rrainey/tempo-bt/images/Tempo-BT-axes.png

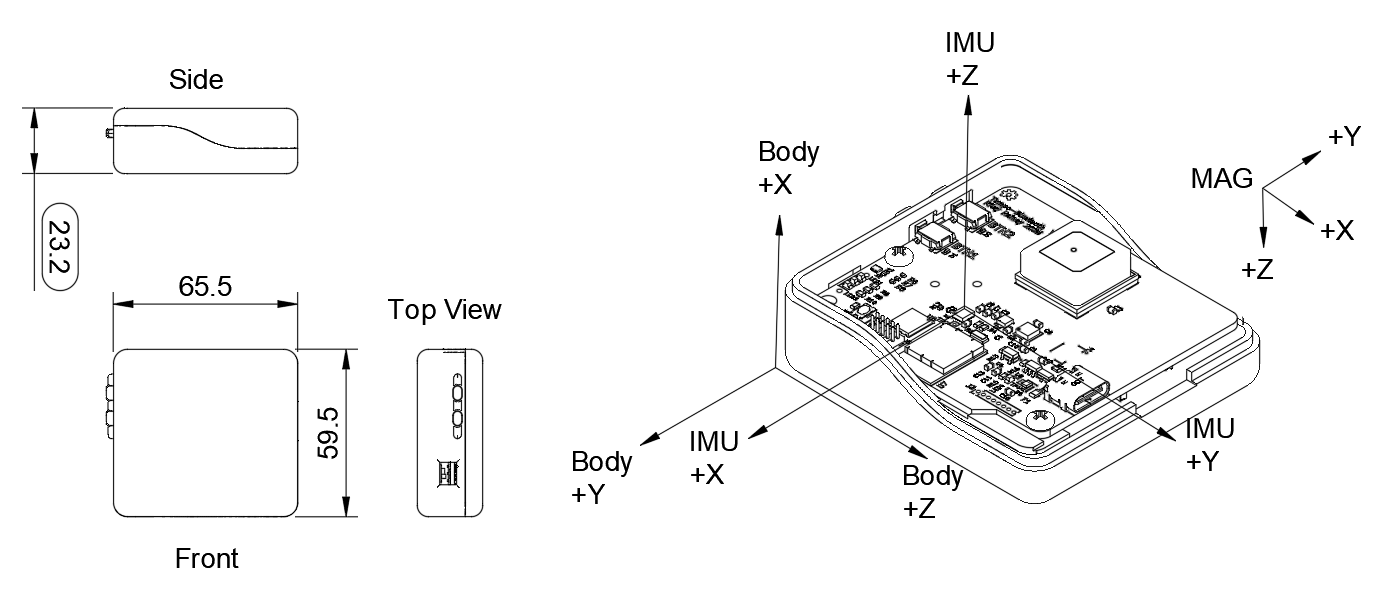
images/Tempo-BT-axes.png
