rrainey/tempo-bt/hardware/tempo-bt/tempo-bt.kicad_sch

## KiCad design hardware/tempo-bt/tempo-bt.kicad_sch (2026-01-11)

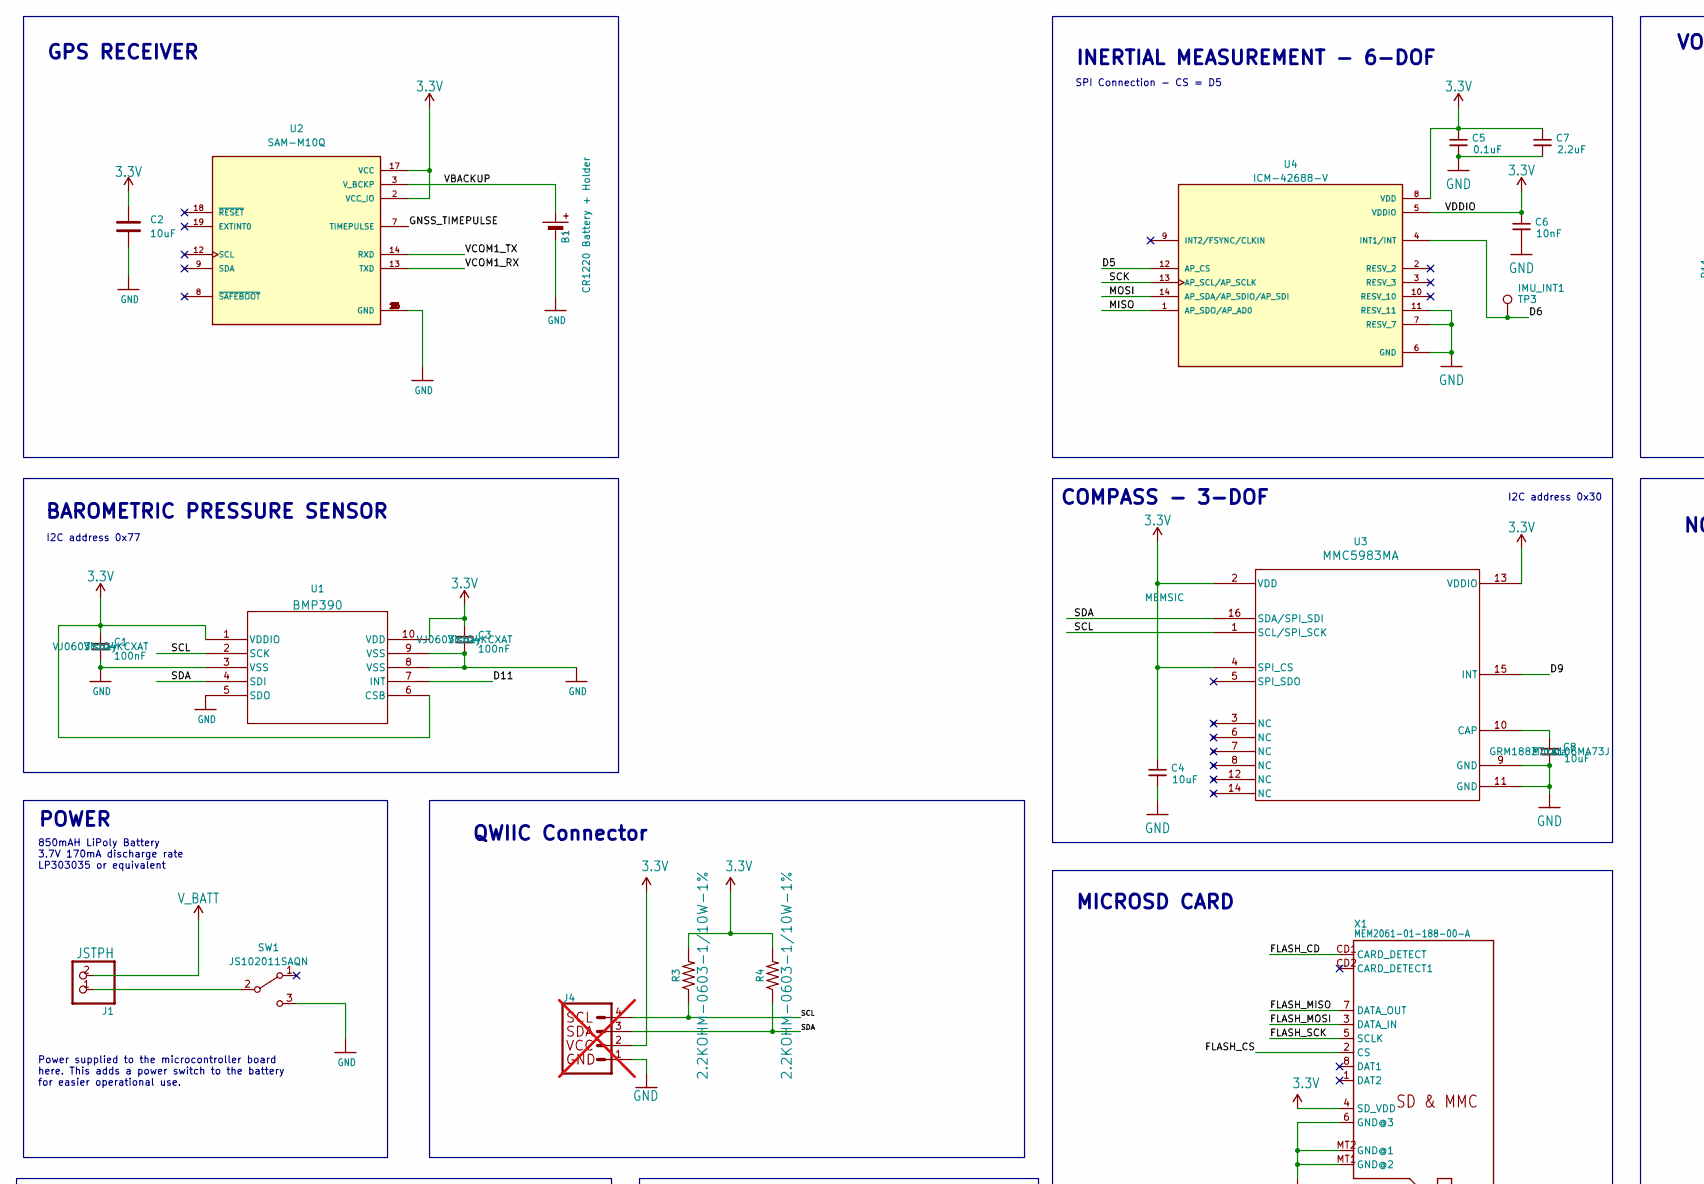
[picture p14: schematic tempo-bt.kicad_sch, part in row 1, column 1]

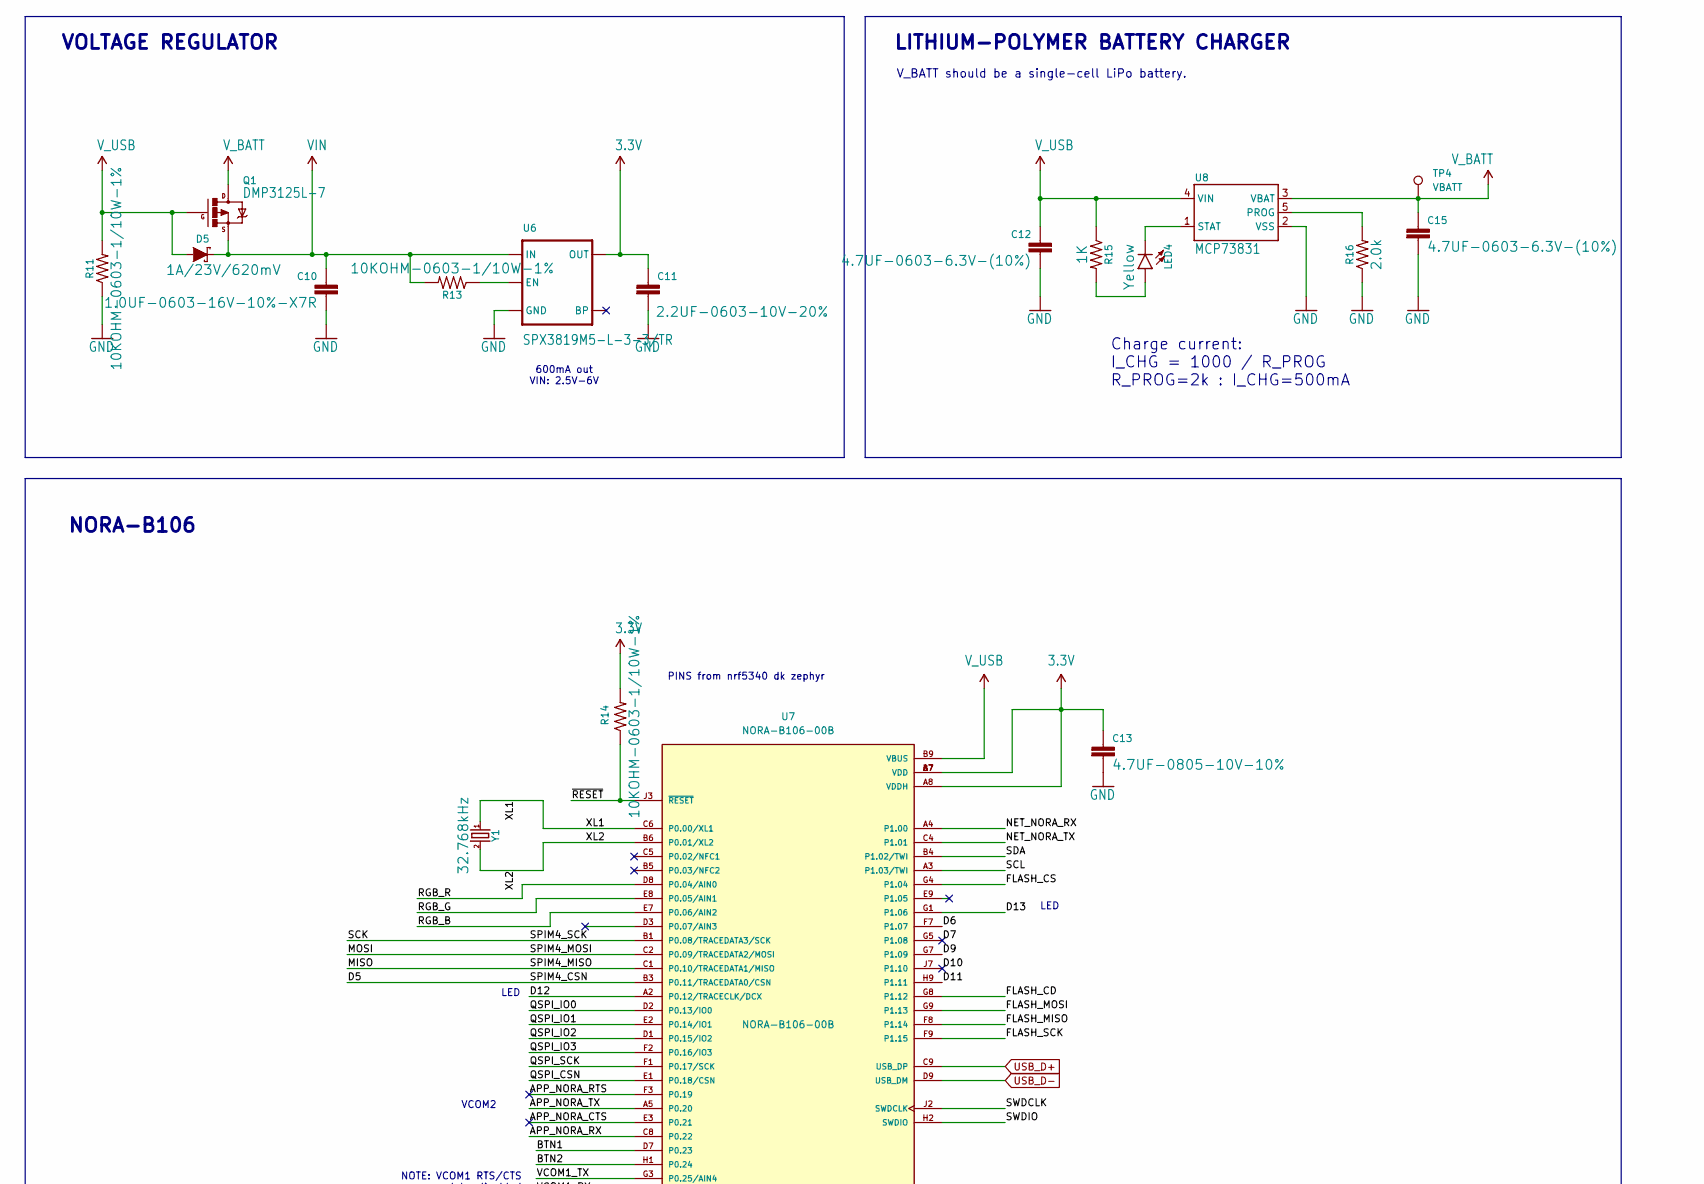
[picture p15: schematic tempo-bt.kicad_sch, part in row 1, column 2]

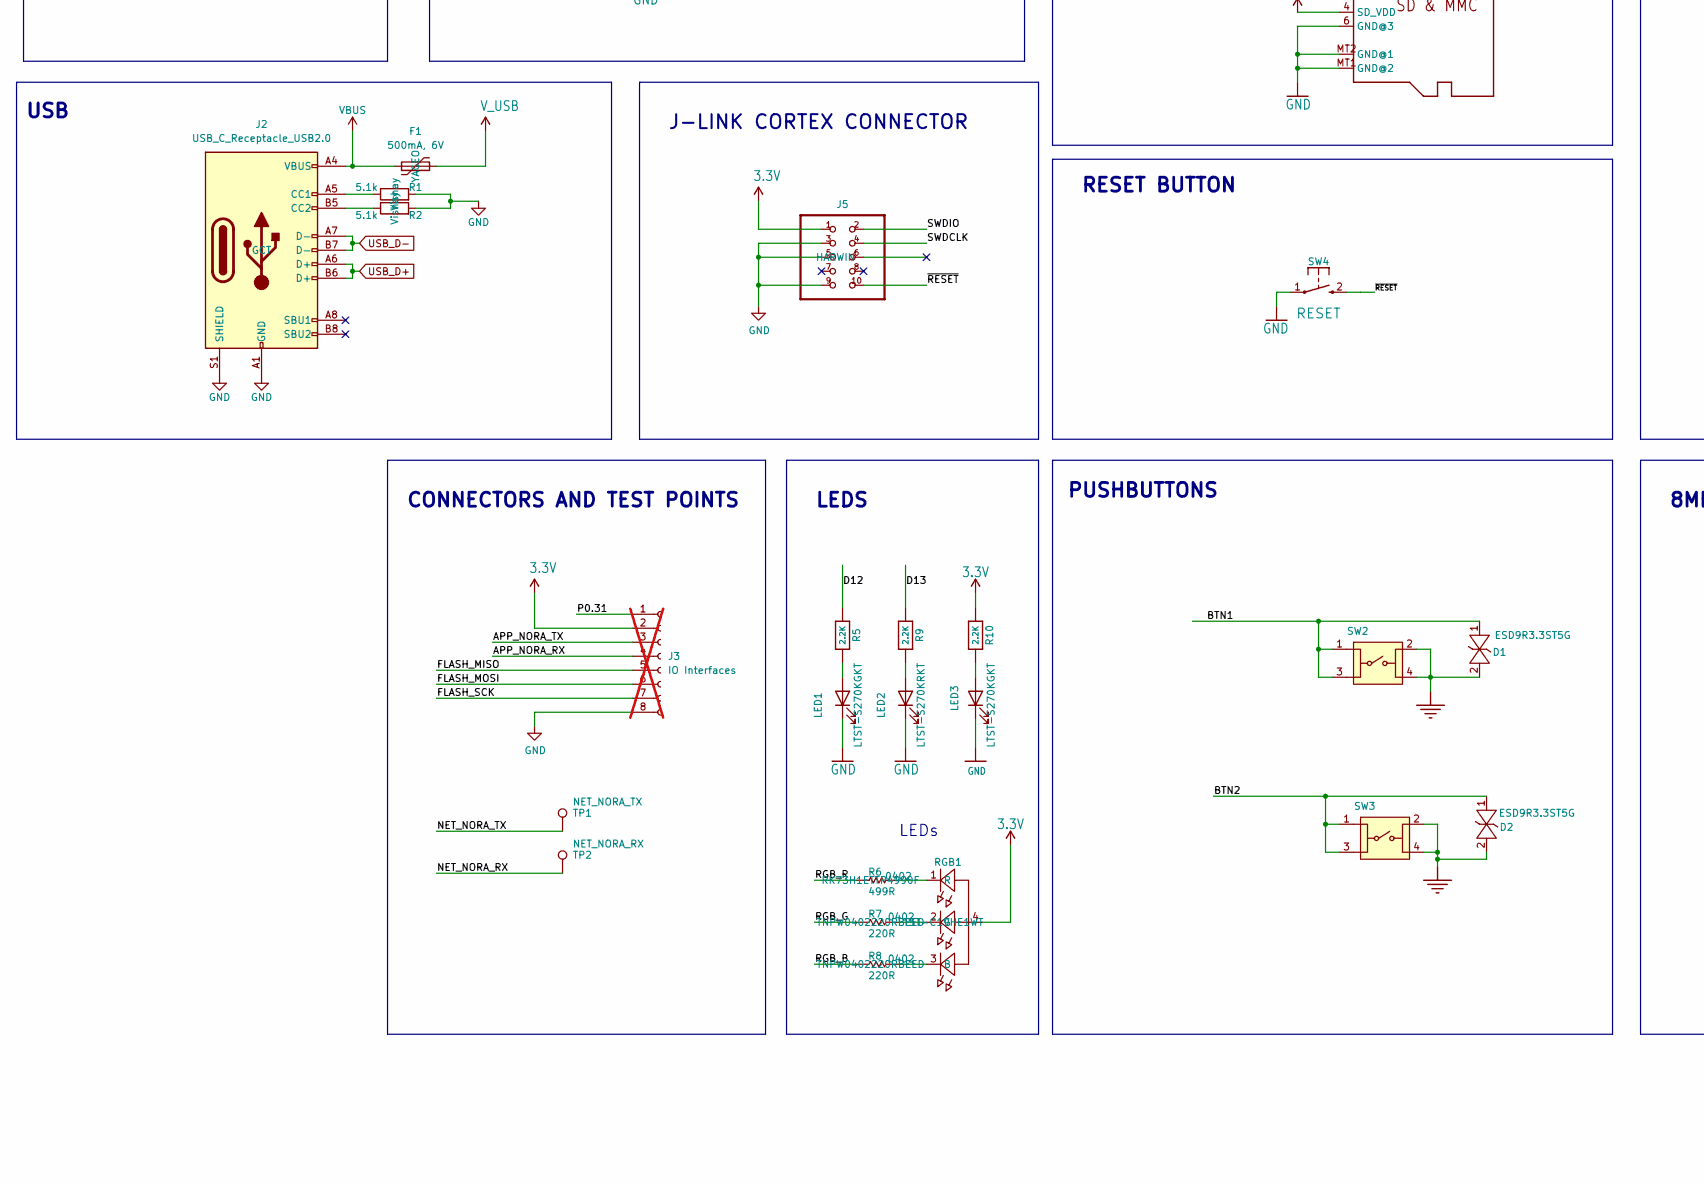
[picture p16: schematic tempo-bt.kicad_sch, part in row 2, column 1]

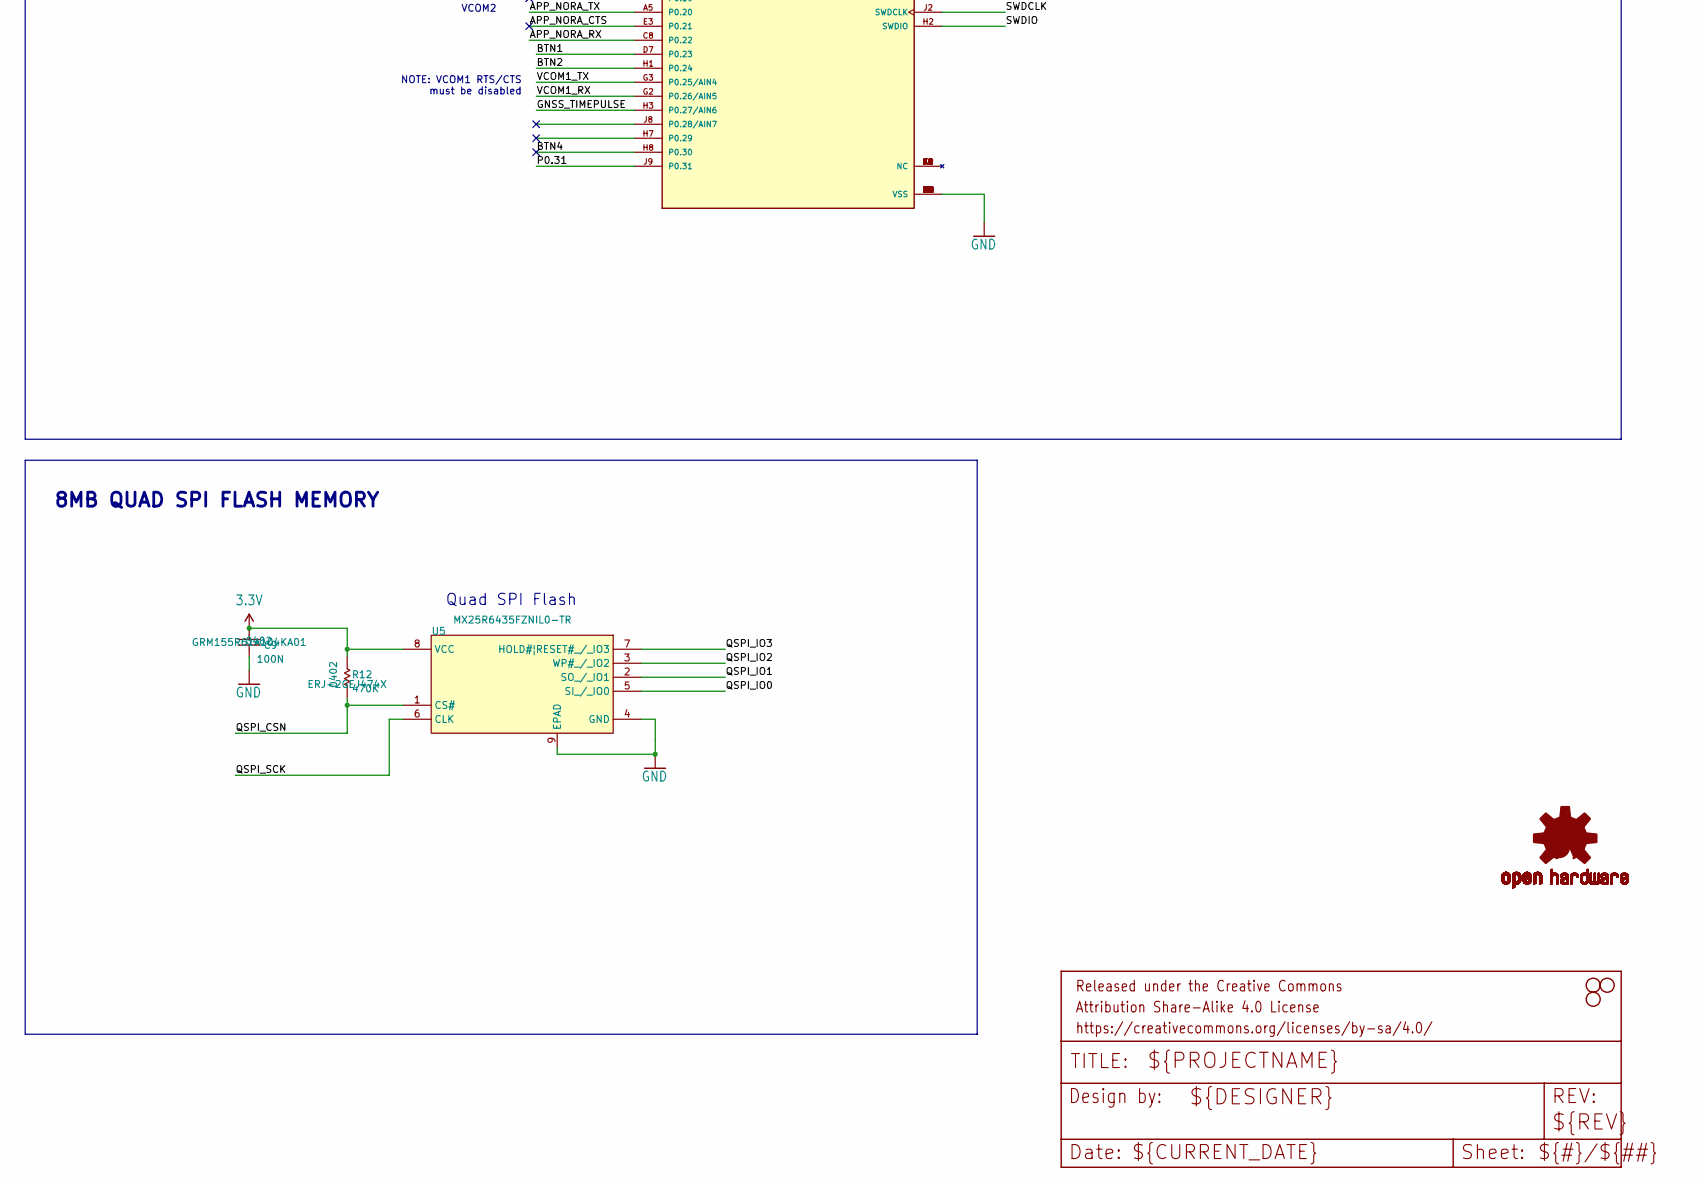
[picture p17: schematic tempo-bt.kicad_sch, part in row 2, column 2]

Parts:
B1: 1056TR; CR1220-2; MPN 1056TR
C1, C3: 100nF; C_0603_1608Metric; MPN VJ0603Y104KCXAT
C2, C4, C8: 10uF; C_0603_1608Metric; MPN GRM188Z71A106MA73J
C5: 0.1uF; C_0603_1608Metric; MPN GRT033C81A104KE01D
C6: 10nF; C_0603_1608Metric; MPN CGA3E2X7R1H103K080AE
C7: 2.2uF; C_0603_1608Metric; MPN GRM188R71A225KE15D
C9: 100nF; C_0402_1005Metric; TOLERANCE 10%; MAX VOLTAGE 10V; PART NUMBER UBXH01-2021002
C10: 1.0UF-0603-16V-10%-X7R; C_0603_1608Metric; MPN 0603DC105KAT2A
C11: 2.2UF-0603-10V-20%; C_0603_1608Metric; MPN GRM188Z71C225KE43D
C12, C15: 4.7UF-0603-6.3V-(10%); C_0603_1608Metric; MPN GRM188Z71A475KE15D
C13: 4.7UF-0805-10V-10%; 0805; MPN GRM21BR71A475KE51L
D1, D2: UBXH07-0000034${DNP}; D_SOD-923; PART NUMBER UBXH07-0000034
D5: 1A/23V/620mV; SOD-323; MPN BAT20JFILM
F1: 500mA, 6V; Fuse_0805_2012Metric; MPN SMD0805B050TF; JLCPCB Part # C269104
FRAME1: FRAME-LETTER; CREATIVE_COMMONS
H1, H2, H3: STAND-OFFTIGHT; STAND-OFF-TIGHT
J1: JSTPH; JSTPH2; Manufacturer Part S2B-PH-SM4-TB
J2: USB_C_Receptacle_USB2.0; GCT-USB4105-GF-A modified-USB-C 16P; MPN USB4105-GF-A-120; JLCPCB Part # C168688
J3: IO Interfaces; PinHeader_1x08_P1.27mm_Vertical; not fitted
J4: QWIIC_CONNECTORJS-1MM; JST04_1MM_RA; MPN SM04B-SRSS-TB; not fitted
J5: 2x5 PTH ARM CORTEX DEBUG; 2X5-PTH-1.27MM-NO_SILK; MPN M50-3500542
LED1, LED3: LTST-S270KGKT; LED_0603_1608Metric; MPN LTST-S270KGKT
LED2: LTST-S270KRKT; LED_0603_1608Metric; MPN LTST-S270KRKT
LED4: Yellow; LED-0603; MPN LTST-S270YKT
LOGO1: OSHW-LOGOS; OSHW-LOGO-S
Q1: DMP3125L-7; SOT23-3@1; MPN DMP3125L-7
R1, R2: 5.1k; R_0402_1005Metric; MPN RCC04025K10FKED; JLCPCB Part # C25905
R3, R4: 2.2KOHM-0603-1/10W-1%; 0603; MPN ERJ-H3EF2201V
R5, R9, R10: 2.2K; R_0603_1608Metric; MPN ERJ-H3EF2201V
R6: 499OHM-0402; R_0402_1005Metric; TOLERANCE 1%; PART NUMBER UBXH18-0000269
R7, R8: 220OHM-0402; R_0402_1005Metric; TOLERANCE 5%; PART NUMBER UBXH18-0008033
R11, R13, R14: 10KOHM-0603-1/10W-1%; 0603; MPN ERJ-H3EF1002V
R12: 470KOHM; R_0402_1005Metric; TOLERANCE 5%; PART NUMBER UBXH18-0008113
R15: 1K; 0603; MPN MR06X1001FTL
R16: 2.0k; 0603; MPN MR06X2001FTL
RGB1: LTST-C19HE1WT; MAX VOLTAGE 5V; PART NUMBER UBXH11-0000058
SW1: JS102011SAQN; MPN JS102011SAQN
SW2, SW3: PTS850; PTS850-with-bosses; PART NUMBER UBXH19-0000035
SW4: RESET; SW_Push_1P1T_NO_CK_KMR2; MPN KMR221NG LFS
TP1: NET_NORA_TX; TestPoint_Pad_1.0x1.0mm
TP2: NET_NORA_RX; TestPoint_Pad_1.0x1.0mm
TP3: IMU_INT1; TestPoint_THTPad_1.0x1.0mm_Drill0.5mm
TP4: VBATT; TestPoint_THTPad_1.0x1.0mm_Drill0.5mm
U1: BMP390; LGA10_BMP390_BOS; MPN BMP390
U2: SAM-M10Q; MODULE_SAM-M8Q-0-10; PARTREV R07
U3: MMC5983MA; MMC5983MA_MEM; MPN MMC5983MA
U4: ICM-42688-V; PQFN50P300X250X97-14N; PARTREV 1.2
U5: MX25R64; WSON-8-1EP_6x5mm_P1.27mm_EP3.4x4mm; PART NUMBER UBXH13-0000138
U6: SPX3819M5-L-3-3/TR; SOT23-5; MPN SPX3819M5-L-3-3/TR
U7: NORA-B106-00B; XCVR_NORA-B106-00B; PARTREV R05
U8: MCP73831; SOT23-5; MPN MCP73831T-4ADI/OT
X1: MEM2061-01-188-00-A; MICROSD; MPN MEM2061-01-188-00-A
Y1: 32.768kHz; CRYSTAL-SMD-3.2X1.5MM; MPN ABS07-120-32.768KHZ-T

Connections:
3.3V: C1.1, C2.1, C3.1, C4.1, C5.1, C6.1, C7.1, C9.1, C11.1, C13.1, J3.2, J4.2, J5.1, R3.2, R4.2, R10.1, R12.2, R14.2, RGB1.4 (A), U1.1 (VDDIO), U1.6 (CSB), U1.10 (VDD), U2.2 (VCC_IO), U2.17 (VCC), U3.2 (VDD), U3.4 (SPI_CS), U3.13 (VDDIO), U4.5 (VDDIO), U4.8 (VDD), U5.8 (VCC), U6.5 (OUT), U7.A7 (VDD), U7.A8 (VDDH), U7.B7 (VDD), X1.4 (SD_VDD)
APP_NORA_CTS: U7.E3 (P0.21)
APP_NORA_RTS: U7.F3 (P0.19)
APP_NORA_RX: J3.4, U7.C8 (P0.22)
APP_NORA_TX: J3.3, U7.A5 (P0.20)
BTN1: D1.1, SW2.1, SW2.3, U7.D7 (P0.23)
BTN2: D2.1, SW3.1, SW3.3, U7.H1 (P0.24)
BTN4: U7.H8 (P0.30)
D5: U4.12 (AP_CS), U7.B3 (P0.11/TRACEDATA0/CSN)
D6: TP3.1, U4.4 (INT1/INT), U7.F7 (P1.07)
D7: U7.G5 (P1.08)
D9: U3.15 (INT), U7.G7 (P1.09)
D10: U7.J7 (P1.10)
D11: U1.7 (INT), U7.H9 (P1.11)
D12: R5.1, U7.A2 (P0.12/TRACECLK/DCX)
D13: R9.1, U7.G1 (P1.06)
FLASH_CD: U7.G8 (P1.12), X1.CD1 (CARD_DETECT)
FLASH_CS: U7.G4 (P1.04), X1.2 (CS)
FLASH_MISO: J3.5, U7.F8 (P1.14), X1.7 (DATA_OUT)
FLASH_MOSI: J3.6, U7.G9 (P1.13), X1.3 (DATA_IN)
FLASH_SCK: J3.7, U7.F9 (P1.15), X1.5 (SCLK)
GND: B1.-, C1.2, C2.2, C3.2, C4.2, C5.2, C6.2, C7.2, C8.2, C9.2, C10.2, C11.2, C12.2, C13.2, C15.2, D1.2, D2.2, J2.A1 (GND), J2.A12 (GND), J2.B1 (GND), J2.B12 (GND), J2.S1 (SHIELD), J3.8, J4.1, J5.3, J5.5, J5.9, LED1.1 (K), LED2.1 (K), LED3.1 (K), R1.2, R2.2, R11.1, R16.1, SW1.3 (C), SW2.2, SW2.4, SW3.2, SW3.4, SW4.1, U1.3 (VSS), U1.5 (SDO), U1.8 (VSS), U1.9 (VSS), U2.1 (GND), U2.4 (GND), U2.5 (GND), U2.6 (GND), U2.10 (GND), U2.11 (GND), U2.15 (GND), U2.16 (GND), U2.20 (GND), U3.9 (GND), U3.11 (GND), U4.6 (GND), U4.7 (RESV_7), U4.11 (RESV_11), U5.4 (GND), U5.9 (EPAD), U6.2 (GND), U7.A1 (VSS), U7.A9 (VSS), U7.B2 (VSS), U7.B8 (VSS), U7.E4 (VSS), U7.E5 (VSS), U7.F4 (VSS), U7.F5 (VSS), U7.K2 (VSS), U7.K3 (VSS), U7.K5 (VSS), U7.K7 (VSS), U7.K8 (VSS), U7.L1 (VSS), U7.L9 (VSS), U7.M1 (VSS), U7.M2 (VSS), U7.M8 (VSS), U7.M9 (VSS), U8.2 (VSS), X1.6 (GND@3), X1.MT1 (GND@2), X1.MT2 (GND@1)
GNSS_TIMEPULSE: U2.7 (TIMEPULSE), U7.H3 (P0.27/AIN6)
MISO: U4.1 (AP_SDO/AP_AD0), U7.C1 (P0.10/TRACEDATA1/MISO)
MOSI: U4.14 (AP_SDA/AP_SDIO/AP_SDI), U7.C2 (P0.09/TRACEDATA2/MOSI)
NET_NORA_RX: TP2.1, U7.A4 (P1.00)
NET_NORA_TX: TP1.1, U7.C4 (P1.01)
unnamed: C8.1, U3.10 (CAP)
unnamed: J1.1, SW1.2 (B)
unnamed: J2.A5 (CC1), R1.1
unnamed: J2.B5 (CC2), R2.1
unnamed: LED1.2 (A), R5.2
unnamed: LED2.2 (A), R9.2
unnamed: LED3.2 (A), R10.2
unnamed: LED4.A, R15.2
unnamed: LED4.C, U8.1 (STAT)
unnamed: R6.2, RGB1.1 (R)
unnamed: R7.2, RGB1.2 (G)
unnamed: R8.2, RGB1.3 (B)
unnamed: R13.1, U6.3 (EN)
unnamed: R16.2, U8.5 (PROG)
unnamed: U7.A6 (NC), U7.J1 (NC), U7.J4 (NC), U7.J5 (NC), U7.K1 (NC), U7.K9 (NC)
P0.31: J3.1, U7.J9 (P0.31)
QSPI_CSN: R12.1, U5.1 (CS#), U7.E1 (P0.18/CSN)
QSPI_IO0: U5.5 (SI_/_IO0), U7.D2 (P0.13/IO0)
QSPI_IO1: U5.2 (SO_/_IO1), U7.E2 (P0.14/IO1)
QSPI_IO2: U5.3 (WP#_/_IO2), U7.D1 (P0.15/IO2)
QSPI_IO3: U5.7 (HOLD#¦RESET#_/_IO3), U7.F2 (P0.16/IO3)
QSPI_SCK: U5.6 (CLK), U7.F1 (P0.17/SCK)
RGB_B: R8.1, U7.E7 (P0.06/AIN2)
RGB_G: R7.1, U7.E8 (P0.05/AIN1)
RGB_R: R6.1, U7.D8 (P0.04/AIN0)
SCK: U4.13 (AP_SCL/AP_SCLK), U7.B1 (P0.08/TRACEDATA3/SCK)
SCL: J4.4, R3.1, U1.2 (SCK), U3.1 (SCL/SPI_SCK), U7.A3 (P1.03/TWI)
SDA: J4.3, R4.1, U1.4 (SDI), U3.16 (SDA/SPI_SDI), U7.B4 (P1.02/TWI)
SWDCLK: J5.4, U7.J2 (SWDCLK)
SWDIO: J5.2, U7.H2 (SWDIO)
USB_D+: J2.A6 (D+), J2.B6 (D+), U7.C9 (USB_DP)
USB_D-: J2.A7 (D-), J2.B7 (D-), U7.D9 (USB_DM)
VBACKUP: B1.+, U2.3 (V_BCKP)
VBUS: F1.1, J2.A4 (VBUS), J2.A9 (VBUS), J2.B4 (VBUS), J2.B9 (VBUS)
VCOM1_RX: U2.13 (TXD), U7.G2 (P0.26/AIN5)
VCOM1_TX: U2.14 (RXD), U7.G3 (P0.25/AIN4)
VIN: C10.1, D5.C, Q1.2 (S), R13.2, U6.1 (IN)
V_BATT: C15.1, J1.2, Q1.3 (D), TP4.1, U8.3 (VBAT)
V_USB: C12.1, D5.A, F1.2, Q1.1 (G), R11.2, R15.1, U7.B9 (VBUS), U8.4 (VIN)
XL1: U7.C6 (P0.00/XL1), Y1.P$1 (1)
XL2: U7.B6 (P0.01/XL2), Y1.P$2 (2)
~RESET: J5.10, R14.1, SW4.2, U7.J3 (~RESET)

Notes on the sheet:
600mA out VIN: 2.5V-6V
GPS RECEIVER
SPI Connection - CS = D5
COMPASS - 3-DOF
BAROMETRIC PRESSURE SENSOR
J-LINK CORTEX CONNECTOR
POWER
V_BATT should be a single-cell LiPo battery.
VOLTAGE REGULATOR
Charge current: I_CHG = 1000 / R_PROG R_PROG=2k : I_CHG=500mA
LED
INERTIAL MEASUREMENT - 6-DOF
LEDs
CONNECTORS AND TEST POINTS
850mAH LiPoly Battery 3.7V 170mA discharge rate LP303035 or equivalent
Power supplied to the microcontroller board here. This adds a power switch to the battery for easier operational use.
PUSHBUTTONS
QWIIC Connector
MICROSD CARD
LITHIUM-POLYMER BATTERY CHARGER
RESET BUTTON
Quad SPI Flash
VCOM2
NOTE: VCOM1 RTS/CTS must be disabled
USB
I2C address 0x77
I2C address 0x30
8MB QUAD SPI FLASH MEMORY
NORA-B106
PINS from nrf5340 dk zephyr
LEDS
