rrainey/tempo-bt/zephyr/tempo-bt-v1/src/mcumgr_custom.c

/*
 * SPDX-License-Identifier: Apache-2.0
 * 
 * Tempo-BT V1 - Custom mcumgr Handlers
 */

#include <string.h>
#include <zephyr/kernel.h>
#include <zephyr/logging/log.h>
#include <zephyr/mgmt/mcumgr/mgmt/mgmt.h>
#include <zephyr/mgmt/mcumgr/smp/smp.h>
#include <zephyr/mgmt/mcumgr/mgmt/handlers.h>
//#include <zephyr/mgmt/mcumgr/util/zcbor_bulk.h>

#include <zcbor_encode.h>
#include <zcbor_decode.h>

#include "services/storage.h"
#include "services/logger.h"
#include "services/led.h"
#include "services/timebase.h"
#include "services/mag.h"
#include "config/settings.h"
#include "ble_mcumgr.h"
#include "generated/app_version.h"

LOG_MODULE_REGISTER(mcumgr_custom, LOG_LEVEL_INF);

/*
 * Test Alarm State Machine
 *
 * Used by TEMPO_MGMT_ID_TEST_LOGGING to synchronize logging start
 * across multiple Tempo-BT devices using the GNSS PPS signal.
 * State values are defined as macros in timebase.h:
 *   TEST_ALARM_IDLE, TEST_ALARM_WAITING_START, TEST_ALARM_WAITING_JUMP
 */

/* Test alarm configuration - accessed by timebase.c via accessor functions */
static struct {
    int state;                     /* TEST_ALARM_IDLE/WAITING_START/WAITING_JUMP */
    uint64_t target_start_utc_ms;  /* UTC time to start logging (ms since epoch) */
    uint32_t jump_delay_sec;       /* Seconds after start to trigger jump (0-3600) */
    uint32_t jump_countdown;       /* Current countdown in seconds */
} test_alarm = {
    .state = TEST_ALARM_IDLE,
    .target_start_utc_ms = 0,
    .jump_delay_sec = 0,
    .jump_countdown = 0
};

/*
 * Test alarm accessor functions - called from timebase.c PPS handler
 */

/* Get current test alarm state */
int test_alarm_get_state(void)
{
    return test_alarm.state;
}

/* Get target start time in UTC milliseconds */
uint64_t test_alarm_get_target_utc_ms(void)
{
    return test_alarm.target_start_utc_ms;
}

/* Get jump delay in seconds */
uint32_t test_alarm_get_jump_delay(void)
{
    return test_alarm.jump_delay_sec;
}

/* Get current jump countdown value */
uint32_t test_alarm_get_jump_countdown(void)
{
    return test_alarm.jump_countdown;
}

/* Set test alarm state */
void test_alarm_set_state(int state)
{
    test_alarm.state = state;
}

/* Initialize jump countdown from delay value */
void test_alarm_start_jump_countdown(void)
{
    test_alarm.jump_countdown = test_alarm.jump_delay_sec;
}

/* Decrement jump countdown, returns new value */
uint32_t test_alarm_decrement_countdown(void)
{
    if (test_alarm.jump_countdown > 0) {
        test_alarm.jump_countdown--;
    }
    return test_alarm.jump_countdown;
}

/* Custom group ID */
#define MGMT_GROUP_ID_TEMPO    64

/* Command IDs */
#define TEMPO_MGMT_ID_SESSION_LIST     0
#define TEMPO_MGMT_ID_SESSION_INFO     1
#define TEMPO_MGMT_ID_STORAGE_INFO     2
#define TEMPO_MGMT_ID_LED_CONTROL      3
#define TEMPO_MGMT_ID_LOGGER_CONTROL   4
#define TEMPO_MGMT_ID_SESSION_DELETE   5
#define TEMPO_MGMT_ID_SETTINGS_GET     6
#define TEMPO_MGMT_ID_SETTINGS_SET     7
#define TEMPO_MGMT_ID_GET_DATETIME     8
#define TEMPO_MGMT_ID_TEST_LOGGING     9
#define TEMPO_MGMT_ID_MAG_CAL_GET    10
#define TEMPO_MGMT_ID_MAG_CAL_SET    11

/*
 * Session listing
 *
 * A session key is "<YYYYMMDD>/<SESSIONID>" — the path of a session
 * directory relative to /logs. Hosts reconstruct file paths from the key
 * by convention (e.g. "/logs/<key>/flight.txt"); see create_session_directory()
 * in logger.c for the layout.
 *
 * Output is paged: the request may carry an optional {"page": uint}
 * (default 0) and the response reports "total_pages". Sessions are ordered
 * by date directory descending (newest first), then by session directory
 * name ascending within each date; both are plain character sorts.
 */

/* One page must fit CONFIG_MCUMGR_TRANSPORT_NETBUF_SIZE */
#define TEMPO_SESSION_LIST_PAGE_SIZE     64
#define TEMPO_SESSION_LIST_MAX_DATES     64
#define TEMPO_SESSION_LIST_MAX_PER_DATE  64
#define TEMPO_SESSION_NAME_LEN           16

/* Directory-name collection: stores the final path element of each
 * subdirectory into a caller-provided fixed-size array */
struct name_collect_context {
    char (*names)[TEMPO_SESSION_NAME_LEN];
    int max;
    int count;
    bool overflow;
};

static int collect_dir_names_callback(const char *path, bool is_dir, size_t size, void *ctx)
{
    struct name_collect_context *nc = (struct name_collect_context *)ctx;
    const char *base;

    ARG_UNUSED(size);

    if (!is_dir) {
        return 0;  /* Sessions and dates are directories */
    }

    if (nc->count >= nc->max) {
        nc->overflow = true;
        return 1;  /* Stop iteration */
    }

    base = strrchr(path, '/');
    base = (base != NULL) ? base + 1 : path;

    strncpy(nc->names[nc->count], base, TEMPO_SESSION_NAME_LEN - 1);
    nc->names[nc->count][TEMPO_SESSION_NAME_LEN - 1] = '\0';
    nc->count++;

    return 0;  /* Continue */
}

/* Insertion sort of fixed-size name strings; small counts only */
static void sort_names(char names[][TEMPO_SESSION_NAME_LEN], int count, bool descending)
{
    for (int i = 1; i < count; i++) {
        char tmp[TEMPO_SESSION_NAME_LEN];
        int j = i - 1;

        memcpy(tmp, names[i], sizeof(tmp));
        while (j >= 0) {
            int cmp = strcmp(names[j], tmp);

            if (descending ? (cmp >= 0) : (cmp <= 0)) {
                break;
            }
            memcpy(names[j + 1], names[j], TEMPO_SESSION_NAME_LEN);
            j--;
        }
        memcpy(names[j + 1], tmp, sizeof(tmp));
    }
}

/* List logging sessions as "<YYYYMMDD>/<SESSIONID>" keys, one page at a time */
static int tempo_mgmt_session_list(struct smp_streamer *ctxt)
{
    zcbor_state_t *zsd = ctxt->reader->zs;
    zcbor_state_t *zse = ctxt->writer->zs;

    /* Too large for the mcumgr workqueue stack; safe as statics because
     * mcumgr handlers are serialized on that single workqueue */
    static char date_names[TEMPO_SESSION_LIST_MAX_DATES][TEMPO_SESSION_NAME_LEN];
    static char session_names[TEMPO_SESSION_LIST_MAX_PER_DATE][TEMPO_SESSION_NAME_LEN];

    uint32_t page = 0;
    bool ok;

    /* Optional request payload: {"page": uint}; absent/empty map = page 0 */
    if (zcbor_map_start_decode(zsd)) {
        struct zcbor_string key;

        while (zcbor_tstr_decode(zsd, &key)) {
            if (key.len == 4 && memcmp(key.value, "page", 4) == 0) {
                ok = zcbor_uint32_decode(zsd, &page);
            } else {
                ok = zcbor_any_skip(zsd, NULL);
            }
            if (!ok) {
                return MGMT_ERR_EINVAL;
            }
        }
        zcbor_map_end_decode(zsd);
    }

    /* Pass 1: collect and sort date directories, newest first (avoids
     * holding two directories open at once while iterating) */
    struct name_collect_context dates = {
        .names = date_names,
        .max = TEMPO_SESSION_LIST_MAX_DATES,
        .count = 0,
        .overflow = false,
    };

    storage_list_dir("/logs", collect_dir_names_callback, &dates);
    sort_names(date_names, dates.count, true);

    ok = zcbor_tstr_put_lit(zse, "sessions") &&
         zcbor_list_start_encode(zse, TEMPO_SESSION_LIST_PAGE_SIZE);

    if (!ok) {
        return MGMT_ERR_EMSGSIZE;
    }

    /* Pass 2: per date directory, collect and sort session names ascending,
     * then emit the entries that fall inside the requested page while
     * counting every session for the totals */
    const uint32_t first = page * TEMPO_SESSION_LIST_PAGE_SIZE;
    uint32_t total = 0;
    int emitted = 0;
    bool truncated = dates.overflow;

    for (int i = 0; i < dates.count; i++) {
        struct name_collect_context sess = {
            .names = session_names,
            .max = TEMPO_SESSION_LIST_MAX_PER_DATE,
            .count = 0,
            .overflow = false,
        };
        char date_path[32];

        snprintf(date_path, sizeof(date_path), "/logs/%s", date_names[i]);
        storage_list_dir(date_path, collect_dir_names_callback, &sess);
        sort_names(session_names, sess.count, false);
        truncated = truncated || sess.overflow;

        for (int j = 0; j < sess.count; j++, total++) {
            char session_key[2 * TEMPO_SESSION_NAME_LEN];

            if (total < first || emitted >= TEMPO_SESSION_LIST_PAGE_SIZE) {
                continue;
            }

            snprintf(session_key, sizeof(session_key), "%s/%s",
                     date_names[i], session_names[j]);

            ok = zcbor_map_start_encode(zse, 1) &&
                 zcbor_tstr_put_lit(zse, "name") &&
                 zcbor_tstr_put_term(zse, session_key, sizeof(session_key)) &&
                 zcbor_map_end_encode(zse, 1);

            if (!ok) {
                return MGMT_ERR_EMSGSIZE;
            }
            emitted++;
        }
    }

    uint32_t total_pages = (total + TEMPO_SESSION_LIST_PAGE_SIZE - 1) /
                           TEMPO_SESSION_LIST_PAGE_SIZE;

    ok = zcbor_list_end_encode(zse, TEMPO_SESSION_LIST_PAGE_SIZE) &&
         zcbor_tstr_put_lit(zse, "count") &&
         zcbor_int32_put(zse, emitted) &&
         zcbor_tstr_put_lit(zse, "page") &&
         zcbor_uint32_put(zse, page) &&
         zcbor_tstr_put_lit(zse, "total_pages") &&
         zcbor_uint32_put(zse, total_pages) &&
         zcbor_tstr_put_lit(zse, "total_sessions") &&
         zcbor_uint32_put(zse, total) &&
         zcbor_tstr_put_lit(zse, "truncated") &&
         zcbor_bool_put(zse, truncated);

    if (!ok) {
        return MGMT_ERR_EMSGSIZE;
    }

    return 0;
}

struct delete_context {
    int error;
    int files_deleted;
};

/* Callback for deleting files in a directory */
static int delete_files_callback(const char *path, bool is_dir, size_t size, void *ctx)
{
    struct delete_context *del_ctx = (struct delete_context *)ctx;
    
    if (!is_dir) {
        /* Delete file */
        int ret = storage_delete(path);
        if (ret != 0 && ret != -ENOENT) {
            LOG_ERR("Failed to delete file %s: %d", path, ret);
            del_ctx->error = ret;
            return -1;  /* Stop on error */
        }
        del_ctx->files_deleted++;
        LOG_DBG("Deleted file: %s", path);
    }
    return 0;  /* Continue */
}

/* Delete a logging session */
static int tempo_mgmt_session_delete(struct smp_streamer *ctxt)
{
    zcbor_state_t *zsd = ctxt->reader->zs;  /* Decoder for request */
    zcbor_state_t *zse = ctxt->writer->zs;  /* Encoder for response */
    
    bool ok;
    struct zcbor_string key;
    struct zcbor_string session_name;
    bool has_session = false;
    
    /* Start decoding the map */
    ok = zcbor_map_start_decode(zsd);
    if (!ok) {
        LOG_ERR("Failed to start decoding map");
        return MGMT_ERR_EINVAL;
    }
    
    /* Decode the session parameter */
    while (zcbor_tstr_decode(zsd, &key)) {
        if (key.len == 7 && memcmp(key.value, "session", 7) == 0) {
            ok = zcbor_tstr_decode(zsd, &session_name);
            if (ok) {
                has_session = true;
            }
        } else {
            /* Skip unknown keys */
            ok = zcbor_any_skip(zsd, NULL);
        }
        
        if (!ok) {
            LOG_ERR("Failed to decode value");
            return MGMT_ERR_EINVAL;
        }
    }
    
    ok = zcbor_map_end_decode(zsd);
    if (!ok) {
        LOG_ERR("Failed to end decoding map");
        return MGMT_ERR_EINVAL;
    }
    
    if (!has_session) {
        LOG_ERR("Missing session parameter");
        return MGMT_ERR_EINVAL;
    }
    
    /* Build the full path to the session directory */
    char session_path[256];
    snprintf(session_path, sizeof(session_path), "/logs/%.*s", 
             (int)session_name.len, session_name.value);
    
    LOG_INF("Deleting session: %s", session_path);
    
    /* Check if currently logging to this session */
    logger_state_t current_state = logger_get_state();
    if (current_state == LOGGER_STATE_LOGGING) {
        uint32_t session_id;
        uint64_t start_time;
        char current_session_path[256];
        
        if (logger_get_session_info(&session_id, &start_time, 
                                   current_session_path, sizeof(current_session_path)) == 0) {
            /* Check if trying to delete active session */
            if (strstr(current_session_path, session_path) != NULL) {
                LOG_ERR("Cannot delete active logging session");
                
                /* Return error response */
                ok = zcbor_tstr_put_lit(zse, "success") &&
                     zcbor_bool_put(zse, false) &&
                     zcbor_tstr_put_lit(zse, "error") &&
                     zcbor_tstr_put_lit(zse, "Session is currently active");
                
                if (!ok) {
                    return MGMT_ERR_EMSGSIZE;
                }
                
                return 0;  /* Return success with error in response */
            }
        }
    }
    
    /* Delete all files in the session directory */
    struct delete_context del_ctx = {0, 0};
    
    /* First pass: delete all files in the directory */
    storage_list_dir(session_path, delete_files_callback, &del_ctx);
    
    if (del_ctx.error != 0) {
        LOG_ERR("Error deleting session files");
        return MGMT_ERR_EUNKNOWN;
    }
    
    /* Delete the session directory itself */
    int ret = storage_delete(session_path);
    if (ret != 0 && ret != -ENOENT) {
        LOG_ERR("Failed to delete session directory: %d", ret);
        /* Continue anyway - we deleted the files */
    }
    
    /* Build success response */
    ok = zcbor_tstr_put_lit(zse, "success") &&
         zcbor_bool_put(zse, true) &&
         zcbor_tstr_put_lit(zse, "files_deleted") &&
         zcbor_int32_put(zse, del_ctx.files_deleted);
    
    if (!ok) {
        return MGMT_ERR_EMSGSIZE;
    }
    
    LOG_INF("Session deleted successfully: %.*s (%d files)", 
            (int)session_name.len, session_name.value, del_ctx.files_deleted);
    
    return 0;
}

/* Get storage info */
static int tempo_mgmt_storage_info(struct smp_streamer *ctxt)
{
    zcbor_state_t *zse = ctxt->writer->zs;
    uint64_t free_bytes, total_bytes;
    int ret;

    ret = storage_get_free_space(&free_bytes, &total_bytes);
    if (ret != 0) {
        return MGMT_ERR_EUNKNOWN;
    }

    uint32_t used_percent = (uint32_t)(100 - (free_bytes * 100 / total_bytes));
    
    /* Get backend type */
    storage_backend_t backend = storage_get_backend();
    const char *backend_str = (backend == STORAGE_BACKEND_FATFS) ? "sdcard" : "internal";

    bool ok = zcbor_tstr_put_lit(zse, "backend") &&
              zcbor_tstr_put_term(zse, backend_str, 10) &&
              zcbor_tstr_put_lit(zse, "free_bytes") &&
              zcbor_uint64_put(zse, free_bytes) &&
              zcbor_tstr_put_lit(zse, "total_bytes") &&
              zcbor_uint64_put(zse, total_bytes) &&
              zcbor_tstr_put_lit(zse, "used_percent") &&
              zcbor_uint32_put(zse, used_percent);

    if (!ok) {
        return MGMT_ERR_EMSGSIZE;
    }

    return 0;
}

/* Logger control command handler */
static int tempo_mgmt_logger_control(struct smp_streamer *ctxt)
{
    zcbor_state_t *zsd = ctxt->reader->zs;  /* Decoder for request */
    zcbor_state_t *zse = ctxt->writer->zs;  /* Encoder for response */
    
    bool ok;
    struct zcbor_string key;
    struct zcbor_string action_str;
    bool has_action = false;
    
    /* Start decoding the map */
    ok = zcbor_map_start_decode(zsd);
    if (!ok) {
        LOG_ERR("Failed to start decoding map");
        return MGMT_ERR_EINVAL;
    }
    
    /* Decode the action parameter */
    while (zcbor_tstr_decode(zsd, &key)) {
        if (key.len == 6 && memcmp(key.value, "action", 6) == 0) {
            ok = zcbor_tstr_decode(zsd, &action_str);
            if (ok) {
                has_action = true;
            }
        } else {
            /* Skip unknown keys */
            ok = zcbor_any_skip(zsd, NULL);
        }
        
        if (!ok) {
            LOG_ERR("Failed to decode value");
            return MGMT_ERR_EINVAL;
        }
    }
    
    ok = zcbor_map_end_decode(zsd);
    if (!ok) {
        LOG_ERR("Failed to end decoding map");
        return MGMT_ERR_EINVAL;
    }
    
    if (!has_action) {
        LOG_ERR("Missing action parameter");
        return MGMT_ERR_EINVAL;
    }
    
    /* Process the action */
    int ret = 0;
    logger_state_t current_state = logger_get_state();
    logger_state_t new_state = current_state;
    bool started_via_ble = false;  /* Track if we started logging from this BLE command */
    
    if (action_str.len == 5 && memcmp(action_str.value, "start", 5) == 0) {
        /* Start logging */
        if (current_state == LOGGER_STATE_ARMED) {
            ret = logger_start("ble_commanded_start");
            if (ret == 0) {
                new_state = LOGGER_STATE_LOGGING;
                started_via_ble = true;
            }
        } else if (current_state == LOGGER_STATE_IDLE) {
            /* Auto-arm then start */
            ret = logger_arm();
            if (ret == 0) {
                ret = logger_start("ble_commanded_start");
                if (ret == 0) {
                    new_state = LOGGER_STATE_LOGGING;
                    started_via_ble = true;
                }
            }
        } else {
            LOG_WRN("Cannot start logging from state %d", current_state);
            ret = -EINVAL;
        }
    } else if (action_str.len == 4 && memcmp(action_str.value, "stop", 4) == 0) {
        /* Stop logging */
        if (current_state == LOGGER_STATE_LOGGING) {
            ret = logger_stop();
            if (ret == 0) {
                new_state = LOGGER_STATE_IDLE;
            }
        } else {
            LOG_WRN("Not logging, cannot stop");
            ret = -EINVAL;
        }
    } else if (action_str.len == 3 && memcmp(action_str.value, "arm", 3) == 0) {
        /* Arm logger */
        if (current_state == LOGGER_STATE_IDLE) {
            ret = logger_arm();
            if (ret == 0) {
                new_state = LOGGER_STATE_ARMED;
            }
        } else {
            LOG_WRN("Cannot arm from state %d", current_state);
            ret = -EINVAL;
        }
    } else if (action_str.len == 6 && memcmp(action_str.value, "disarm", 6) == 0) {
        /* Disarm logger */
        if (current_state == LOGGER_STATE_ARMED) {
            ret = logger_disarm();
            if (ret == 0) {
                new_state = LOGGER_STATE_IDLE;
            }
        } else {
            LOG_WRN("Cannot disarm from state %d", current_state);
            ret = -EINVAL;
        }
    } else {
        LOG_ERR("Unknown action: %.*s", action_str.len, action_str.value);
        return MGMT_ERR_EINVAL;
    }
    
    if (ret != 0) {
        return MGMT_ERR_EUNKNOWN;
    }

    /*
     * BLE-initiated logging start (issue #2):
     * logger_start() already called ble_mcumgr_stop() which killed the radio.
     * We need to briefly re-enable BLE so this mcumgr response can be sent,
     * then schedule a deferred stop (500ms) to shut it down again.
     */
    if (started_via_ble) {
        ble_mcumgr_restart();
        ble_mcumgr_stop_deferred();
    }
    
    /* Build response with current state and session info */
    const char *state_str = "unknown";
    switch (new_state) {
        case LOGGER_STATE_IDLE:       state_str = "idle"; break;
        case LOGGER_STATE_ARMED:      state_str = "armed"; break;
        case LOGGER_STATE_LOGGING:    state_str = "logging"; break;
        case LOGGER_STATE_JUMPED:    state_str = "jumped"; break;
        case LOGGER_STATE_POSTFLIGHT: state_str = "postflight"; break;
        case LOGGER_STATE_ERROR:      state_str = "error"; break;
    }
    
    ok = zcbor_tstr_put_lit(zse, "state") &&
         zcbor_tstr_put_term(zse, state_str, 10) &&
         zcbor_tstr_put_lit(zse, "success") &&
         zcbor_bool_put(zse, true);
    
    /* If logging, add session info */
    if (new_state == LOGGER_STATE_LOGGING) {
        uint32_t session_id;
        uint64_t start_time;
        char path[256];
        
        if (logger_get_session_info(&session_id, &start_time, path, sizeof(path)) == 0) {
            ok = ok && zcbor_tstr_put_lit(zse, "session_id") &&
                 zcbor_uint32_put(zse, session_id) &&
                 zcbor_tstr_put_lit(zse, "session_path") &&
                 zcbor_tstr_put_term(zse, path, sizeof(path));
        }
    }
    
    if (!ok) {
        return MGMT_ERR_EMSGSIZE;
    }
    
    LOG_INF("Logger control: action=%.*s, new_state=%s", 
            action_str.len, action_str.value, state_str);
    
    return 0;
}

/* LED control command handler */
static int tempo_mgmt_led_control(struct smp_streamer *ctxt)
{
    zcbor_state_t *zsd = ctxt->reader->zs;  /* Decoder for request */
    zcbor_state_t *zse = ctxt->writer->zs;  /* Encoder for response */
    
    bool ok;
    bool enable = false;
    uint32_t r = 0, g = 0, b = 0;
    bool has_enable = false;
    bool has_r = false, has_g = false, has_b = false;
    struct zcbor_string key;
    
    /* Start decoding the map */
    ok = zcbor_map_start_decode(zsd);
    if (!ok) {
        LOG_ERR("Failed to start decoding map");
        return MGMT_ERR_EINVAL;
    }
    
    /* Decode each key-value pair */
    while (zcbor_tstr_decode(zsd, &key)) {
        if (key.len == 6 && memcmp(key.value, "enable", 6) == 0) {
            ok = zcbor_bool_decode(zsd, &enable);
            if (ok) has_enable = true;
        }
        else if (key.len == 1 && key.value[0] == 'r') {
            ok = zcbor_uint32_decode(zsd, &r);
            if (ok) has_r = true;
        }
        else if (key.len == 1 && key.value[0] == 'g') {
            ok = zcbor_uint32_decode(zsd, &g);
            if (ok) has_g = true;
        }
        else if (key.len == 1 && key.value[0] == 'b') {
            ok = zcbor_uint32_decode(zsd, &b);
            if (ok) has_b = true;
        }
        else {
            /* Skip unknown keys */
            ok = zcbor_any_skip(zsd, NULL);
        }
        
        if (!ok) {
            LOG_ERR("Failed to decode value");
            return MGMT_ERR_EINVAL;
        }
    }
    
    ok = zcbor_map_end_decode(zsd);
    if (!ok) {
        LOG_ERR("Failed to end decoding map");
        return MGMT_ERR_EINVAL;
    }
    
    LOG_INF("LED control: enable=%d, R=%d G=%d B=%d", 
            enable, (uint8_t)r, (uint8_t)g, (uint8_t)b);
    
    /* Validate color values */
    if (r > 255 || g > 255 || b > 255) {
        LOG_ERR("Invalid color values");
        return MGMT_ERR_EINVAL;
    }
    
    /* Apply the command */
    rgb_color_t color = {
        .r = (uint8_t)r,
        .g = (uint8_t)g,
        .b = (uint8_t)b
    };
    
    int ret = led_service_set_override(color, enable);
    if (ret != 0) {
        return MGMT_ERR_EUNKNOWN;
    }
    
    /* Build response with current state */
    rgb_color_t current_color;
    bool override_enabled;
    led_service_get_override(&current_color, &override_enabled);
    
    ok = zcbor_tstr_put_lit(zse, "enabled") &&
         zcbor_bool_put(zse, override_enabled) &&
         zcbor_tstr_put_lit(zse, "r") &&
         zcbor_uint32_put(zse, current_color.r) &&
         zcbor_tstr_put_lit(zse, "g") &&
         zcbor_uint32_put(zse, current_color.g) &&
         zcbor_tstr_put_lit(zse, "b") &&
         zcbor_uint32_put(zse, current_color.b);
    
    if (!ok) {
        return MGMT_ERR_EMSGSIZE;
    }
    
    return 0;
}

/* Get NVM settings */
static int tempo_mgmt_settings_get(struct smp_streamer *ctxt)
{
    zcbor_state_t *zse = ctxt->writer->zs;
    
    /* Get current settings values */
    const char *ble_name = app_settings_get_ble_name();
    bool pps_enabled = app_settings_get_pps_enabled();
    uint8_t pcb_variant = app_settings_get_pcb_variant();
    const char *log_backend = app_settings_get_log_backend();
    
    uint8_t mag_mode = app_settings_get_mag_mode();

    /* Build response with all settings plus firmware identification;
     * version strings are truncated at 31 characters */
    bool ok = zcbor_tstr_put_lit(zse, "ble_name") &&
              zcbor_tstr_put_term(zse, ble_name, 32) &&
              zcbor_tstr_put_lit(zse, "pps_enabled") &&
              zcbor_bool_put(zse, pps_enabled) &&
              zcbor_tstr_put_lit(zse, "pcb_variant") &&
              zcbor_uint32_put(zse, pcb_variant) &&
              zcbor_tstr_put_lit(zse, "log_backend") &&
              zcbor_tstr_put_term(zse, log_backend, 12) &&
              zcbor_tstr_put_lit(zse, "mag_mode") &&
              zcbor_uint32_put(zse, mag_mode) &&
              zcbor_tstr_put_lit(zse, "fw_version") &&
              zcbor_tstr_put_term(zse, APP_VERSION_STRING, 31) &&
              zcbor_tstr_put_lit(zse, "git_commit") &&
              zcbor_tstr_put_term(zse, APP_GIT_COMMIT, 31);

    if (!ok) {
        return MGMT_ERR_EMSGSIZE;
    }

    LOG_INF("Settings get: ble_name=%s, pps=%d, pcb=0x%02X, backend=%s, mag_mode=%u, fw=%s (%s)",
            ble_name, pps_enabled, pcb_variant, log_backend, mag_mode,
            APP_VERSION_STRING, APP_GIT_COMMIT);
    
    return 0;
}

/* Set NVM settings */
static int tempo_mgmt_settings_set(struct smp_streamer *ctxt)
{
    zcbor_state_t *zsd = ctxt->reader->zs;  /* Decoder for request */
    zcbor_state_t *zse = ctxt->writer->zs;  /* Encoder for response */
    
    bool ok;
    struct zcbor_string key;
    struct zcbor_string str_value;
    uint32_t uint_value;
    int ret = 0;
    
    /* Values to update */
    bool has_ble_name = false;
    bool has_pps = false;
    bool has_pcb = false;
    bool has_backend = false;
    bool has_mag_mode = false;

    char new_ble_name[32];
    bool new_pps;
    uint8_t new_pcb = 1;
    char new_backend[12];
    uint8_t new_mag_mode = 0;
    
    /* Start decoding the map */
    ok = zcbor_map_start_decode(zsd);
    if (!ok) {
        LOG_ERR("Failed to start decoding map");
        return MGMT_ERR_EINVAL;
    }
    
    /* Decode each setting */
    while (zcbor_tstr_decode(zsd, &key)) {
        if (key.len == 8 && memcmp(key.value, "ble_name", 8) == 0) {
            ok = zcbor_tstr_decode(zsd, &str_value);
            if (ok && str_value.len < sizeof(new_ble_name)) {
                memcpy(new_ble_name, str_value.value, str_value.len);
                new_ble_name[str_value.len] = '\0';
                has_ble_name = true;
            }
        }
        else if (key.len == 11 && memcmp(key.value, "pps_enabled", 11) == 0) {
            ok = zcbor_bool_decode(zsd, &new_pps);
            if (ok) has_pps = true;
        }
        else if (key.len == 11 && memcmp(key.value, "pcb_variant", 11) == 0) {
            ok = zcbor_uint32_decode(zsd, &uint_value);
            if (ok && uint_value <= 255) {
                new_pcb = (uint8_t)uint_value;
                has_pcb = true;
            }
        }
        else if (key.len == 11 && memcmp(key.value, "log_backend", 11) == 0) {
            ok = zcbor_tstr_decode(zsd, &str_value);
            if (ok && str_value.len < sizeof(new_backend)) {
                memcpy(new_backend, str_value.value, str_value.len);
                new_backend[str_value.len] = '\0';
                has_backend = true;
            }
        }
        else if (key.len == 8 && memcmp(key.value, "mag_mode", 8) == 0) {
            ok = zcbor_uint32_decode(zsd, &uint_value);
            if (ok && uint_value <= 2) {
                new_mag_mode = (uint8_t)uint_value;
                has_mag_mode = true;
            }
        }
        else {
            /* Skip unknown keys */
            ok = zcbor_any_skip(zsd, NULL);
        }
        
        if (!ok) {
            LOG_ERR("Failed to decode value");
            return MGMT_ERR_EINVAL;
        }
    }
    
    ok = zcbor_map_end_decode(zsd);
    if (!ok) {
        LOG_ERR("Failed to end decoding map");
        return MGMT_ERR_EINVAL;
    }
    
    /* Apply the settings */
    if (has_ble_name) {
        ret = app_settings_set_ble_name(new_ble_name);
        if (ret != 0) {
            LOG_ERR("Failed to set ble_name: %d", ret);
            return MGMT_ERR_EUNKNOWN;
        }
        LOG_INF("Set ble_name: %s", new_ble_name);
    }
    
    if (has_pps) {
        ret = app_settings_set_pps_enabled(new_pps);
        if (ret != 0) {
            LOG_ERR("Failed to set pps_enabled: %d", ret);
            return MGMT_ERR_EUNKNOWN;
        }
        LOG_INF("Set pps_enabled: %d", new_pps);
    }
    
    if (has_pcb) {
        ret = app_settings_set_pcb_variant(new_pcb);
        if (ret != 0) {
            LOG_ERR("Failed to set pcb_variant: %d", ret);
            return MGMT_ERR_EUNKNOWN;
        }
        LOG_INF("Set pcb_variant: 0x%02X", new_pcb);
    }
    
    if (has_backend) {
        ret = app_settings_set_log_backend(new_backend);
        if (ret != 0) {
            LOG_ERR("Failed to set log_backend: %d", ret);
            return MGMT_ERR_EUNKNOWN;
        }
        LOG_INF("Set log_backend: %s", new_backend);
    }

    if (has_mag_mode) {
        ret = app_settings_set_mag_mode(new_mag_mode);
        if (ret != 0) {
            LOG_ERR("Failed to set mag_mode: %d", ret);
            return MGMT_ERR_EUNKNOWN;
        }
        LOG_INF("Set mag_mode: %u", new_mag_mode);
    }

    /* Build response with all current settings (after updates) */
    const char *ble_name = app_settings_get_ble_name();
    bool pps_enabled = app_settings_get_pps_enabled();
    uint8_t pcb_variant = app_settings_get_pcb_variant();
    const char *log_backend = app_settings_get_log_backend();
    
    uint8_t mag_mode = app_settings_get_mag_mode();

    ok = zcbor_tstr_put_lit(zse, "ble_name") &&
         zcbor_tstr_put_term(zse, ble_name, 32) &&
         zcbor_tstr_put_lit(zse, "pps_enabled") &&
         zcbor_bool_put(zse, pps_enabled) &&
         zcbor_tstr_put_lit(zse, "pcb_variant") &&
         zcbor_uint32_put(zse, pcb_variant) &&
         zcbor_tstr_put_lit(zse, "log_backend") &&
         zcbor_tstr_put_term(zse, log_backend, 12) &&
         zcbor_tstr_put_lit(zse, "mag_mode") &&
         zcbor_uint32_put(zse, mag_mode) &&
         zcbor_tstr_put_lit(zse, "success") &&
         zcbor_bool_put(zse, true);

    if (has_ble_name) {
        ok = ok && zcbor_tstr_put_lit(zse, "note") &&
             zcbor_tstr_put_lit(zse, "BLE name changes require reboot");
    }
    
    if (!ok) {
        return MGMT_ERR_EMSGSIZE;
    }

    return 0;
}

/* Get current UTC datetime as ISO 8601 string */
static int tempo_mgmt_get_datetime(struct smp_streamer *ctxt)
{
    zcbor_state_t *zse = ctxt->writer->zs;
    char datetime_buf[32];

    LOG_INF("Get datetime handler called");

    int ret = timebase_get_utc_iso8601(datetime_buf, sizeof(datetime_buf));
    if (ret != 0) {
        LOG_WRN("No valid UTC time available (ret=%d)", ret);
        /* No valid UTC time available */
        bool ok = zcbor_tstr_put_lit(zse, "error") &&
                  zcbor_tstr_put_lit(zse, "No valid UTC time") &&
                  zcbor_tstr_put_lit(zse, "datetime") &&
                  zcbor_tstr_put_lit(zse, "");

        if (!ok) {
            return MGMT_ERR_EMSGSIZE;
        }
        return 0;
    }

    bool ok = zcbor_tstr_put_lit(zse, "datetime") &&
              zcbor_tstr_put_term(zse, datetime_buf, sizeof(datetime_buf));

    if (!ok) {
        return MGMT_ERR_EMSGSIZE;
    }

    LOG_INF("Get datetime: %s", datetime_buf);

    return 0;
}

/* Test logging command - schedule synchronized logging start */
static int tempo_mgmt_test_logging(struct smp_streamer *ctxt)
{
    zcbor_state_t *zsd = ctxt->reader->zs;
    zcbor_state_t *zse = ctxt->writer->zs;

    bool ok;
    struct zcbor_string key;
    struct zcbor_string start_str;
    uint32_t jump_value = 0;
    bool has_start = false;
    bool has_jump = false;

    /* Start decoding the map */
    ok = zcbor_map_start_decode(zsd);
    if (!ok) {
        LOG_ERR("Failed to start decoding map");
        return MGMT_ERR_EINVAL;
    }

    /* Decode parameters: {"start": "MMSS", "jump": nn} */
    while (zcbor_tstr_decode(zsd, &key)) {
        if (key.len == 5 && memcmp(key.value, "start", 5) == 0) {
            ok = zcbor_tstr_decode(zsd, &start_str);
            if (ok && start_str.len == 4) {
                has_start = true;
            }
        }
        else if (key.len == 4 && memcmp(key.value, "jump", 4) == 0) {
            ok = zcbor_uint32_decode(zsd, &jump_value);
            if (ok) {
                has_jump = true;
            }
        }
        else {
            ok = zcbor_any_skip(zsd, NULL);
        }

        if (!ok) {
            LOG_ERR("Failed to decode value");
            return MGMT_ERR_EINVAL;
        }
    }

    ok = zcbor_map_end_decode(zsd);
    if (!ok) {
        LOG_ERR("Failed to end decoding map");
        return MGMT_ERR_EINVAL;
    }

    if (!has_start) {
        LOG_ERR("Missing 'start' parameter");
        return MGMT_ERR_EINVAL;
    }

    /* Validate jump delay (0-3600 seconds) */
    if (has_jump && jump_value > 3600) {
        LOG_ERR("Jump delay exceeds maximum (3600 seconds)");
        return MGMT_ERR_EINVAL;
    }

    /* Parse MMSS format */
    uint32_t mm = (start_str.value[0] - '0') * 10 + (start_str.value[1] - '0');
    uint32_t ss = (start_str.value[2] - '0') * 10 + (start_str.value[3] - '0');

    if (mm > 59 || ss > 59) {
        LOG_ERR("Invalid start time: %02u:%02u", mm, ss);
        return MGMT_ERR_EINVAL;
    }

    /* Get current UTC time */
    time_correlation_t corr;
    if (!timebase_get_correlation(&corr) || !corr.valid) {
        LOG_ERR("No valid UTC time correlation");
        ok = zcbor_tstr_put_lit(zse, "success") &&
             zcbor_bool_put(zse, false) &&
             zcbor_tstr_put_lit(zse, "error") &&
             zcbor_tstr_put_lit(zse, "No valid UTC time");

        if (!ok) {
            return MGMT_ERR_EMSGSIZE;
        }
        return 0;
    }

    /* Calculate target UTC time in milliseconds */
    uint64_t current_utc_ms = corr.utc_ms;

    /* Get current hour start (truncate to hour boundary) */
    uint64_t ms_per_hour = 3600ULL * 1000ULL;
    uint64_t current_hour_start = (current_utc_ms / ms_per_hour) * ms_per_hour;

    /* Calculate target time within hour */
    uint64_t target_offset_ms = (mm * 60ULL + ss) * 1000ULL;
    uint64_t target_utc_ms = current_hour_start + target_offset_ms;

    /* If target time has passed in current hour, schedule for next hour */
    if (target_utc_ms <= current_utc_ms) {
        target_utc_ms += ms_per_hour;
        LOG_INF("Target time passed, scheduling for next hour");
    }

    /* Calculate seconds until start */
    uint32_t seconds_until_start = (uint32_t)((target_utc_ms - current_utc_ms) / 1000);

    /* Set up the test alarm */
    test_alarm.target_start_utc_ms = target_utc_ms;
    test_alarm.jump_delay_sec = has_jump ? jump_value : 0;
    test_alarm.jump_countdown = 0;
    test_alarm.state = TEST_ALARM_WAITING_START;

    LOG_INF("Test logging scheduled: start=%02u:%02u (%u sec), jump=%u sec",
            mm, ss, seconds_until_start, test_alarm.jump_delay_sec);

    /*
     * TEST_LOGGING schedules a future start via PPS alarm — the actual
     * logger_start() will be called later and will disable BLE at that point.
     * The response goes out now while BLE is still active, so no deferred
     * stop is needed here.
     */

    /* Build response */
    ok = zcbor_tstr_put_lit(zse, "success") &&
         zcbor_bool_put(zse, true) &&
         zcbor_tstr_put_lit(zse, "start_mm") &&
         zcbor_uint32_put(zse, mm) &&
         zcbor_tstr_put_lit(zse, "start_ss") &&
         zcbor_uint32_put(zse, ss) &&
         zcbor_tstr_put_lit(zse, "seconds_until_start") &&
         zcbor_uint32_put(zse, seconds_until_start) &&
         zcbor_tstr_put_lit(zse, "jump_delay") &&
         zcbor_uint32_put(zse, test_alarm.jump_delay_sec);

    if (!ok) {
        return MGMT_ERR_EMSGSIZE;
    }

    return 0;
}

/* Get magnetometer calibration data */
static int tempo_mgmt_mag_cal_get(struct smp_streamer *ctxt)
{
    zcbor_state_t *zse = ctxt->writer->zs;
    mag_calibration_t cal;

    mag_cal_get(&cal);

    bool ok = zcbor_tstr_put_lit(zse, "valid") &&
              zcbor_bool_put(zse, cal.valid) &&
              zcbor_tstr_put_lit(zse, "offset_x") &&
              zcbor_int32_put(zse, cal.offset_x) &&
              zcbor_tstr_put_lit(zse, "offset_y") &&
              zcbor_int32_put(zse, cal.offset_y) &&
              zcbor_tstr_put_lit(zse, "offset_z") &&
              zcbor_int32_put(zse, cal.offset_z) &&
              zcbor_tstr_put_lit(zse, "scale_x") &&
              zcbor_uint32_put(zse, cal.scale_x) &&
              zcbor_tstr_put_lit(zse, "scale_y") &&
              zcbor_uint32_put(zse, cal.scale_y) &&
              zcbor_tstr_put_lit(zse, "scale_z") &&
              zcbor_uint32_put(zse, cal.scale_z);

    if (!ok) {
        return MGMT_ERR_EMSGSIZE;
    }

    LOG_INF("Mag cal get: valid=%d, offsets=[%d,%d,%d], scales=[%u,%u,%u]",
            cal.valid, cal.offset_x, cal.offset_y, cal.offset_z,
            cal.scale_x, cal.scale_y, cal.scale_z);

    return 0;
}

/* Set magnetometer calibration data and persist to NVM */
static int tempo_mgmt_mag_cal_set(struct smp_streamer *ctxt)
{
    zcbor_state_t *zsd = ctxt->reader->zs;
    zcbor_state_t *zse = ctxt->writer->zs;

    bool ok;
    struct zcbor_string key;
    int32_t int_value;
    uint32_t uint_value;
    mag_calibration_t cal = {0};
    bool has_offset_x = false, has_offset_y = false, has_offset_z = false;
    bool has_scale_x = false, has_scale_y = false, has_scale_z = false;

    /* Start decoding the map */
    ok = zcbor_map_start_decode(zsd);
    if (!ok) {
        LOG_ERR("Failed to start decoding map");
        return MGMT_ERR_EINVAL;
    }

    /* Decode each field */
    while (zcbor_tstr_decode(zsd, &key)) {
        if (key.len == 8 && memcmp(key.value, "offset_x", 8) == 0) {
            ok = zcbor_int32_decode(zsd, &int_value);
            if (ok) { cal.offset_x = int_value; has_offset_x = true; }
        }
        else if (key.len == 8 && memcmp(key.value, "offset_y", 8) == 0) {
            ok = zcbor_int32_decode(zsd, &int_value);
            if (ok) { cal.offset_y = int_value; has_offset_y = true; }
        }
        else if (key.len == 8 && memcmp(key.value, "offset_z", 8) == 0) {
            ok = zcbor_int32_decode(zsd, &int_value);
            if (ok) { cal.offset_z = int_value; has_offset_z = true; }
        }
        else if (key.len == 7 && memcmp(key.value, "scale_x", 7) == 0) {
            ok = zcbor_uint32_decode(zsd, &uint_value);
            if (ok && uint_value <= UINT16_MAX) {
                cal.scale_x = (uint16_t)uint_value;
                has_scale_x = true;
            }
        }
        else if (key.len == 7 && memcmp(key.value, "scale_y", 7) == 0) {
            ok = zcbor_uint32_decode(zsd, &uint_value);
            if (ok && uint_value <= UINT16_MAX) {
                cal.scale_y = (uint16_t)uint_value;
                has_scale_y = true;
            }
        }
        else if (key.len == 7 && memcmp(key.value, "scale_z", 7) == 0) {
            ok = zcbor_uint32_decode(zsd, &uint_value);
            if (ok && uint_value <= UINT16_MAX) {
                cal.scale_z = (uint16_t)uint_value;
                has_scale_z = true;
            }
        }
        else {
            /* Skip unknown keys */
            ok = zcbor_any_skip(zsd, NULL);
        }

        if (!ok) {
            LOG_ERR("Failed to decode value");
            return MGMT_ERR_EINVAL;
        }
    }

    ok = zcbor_map_end_decode(zsd);
    if (!ok) {
        LOG_ERR("Failed to end decoding map");
        return MGMT_ERR_EINVAL;
    }

    /* All six fields are required */
    if (!has_offset_x || !has_offset_y || !has_offset_z ||
        !has_scale_x || !has_scale_y || !has_scale_z) {
        LOG_ERR("Missing required calibration fields");
        return MGMT_ERR_EINVAL;
    }

    /* Apply and save */
    cal.valid = true;
    int ret = mag_cal_set(&cal);
    if (ret != 0) {
        LOG_ERR("Failed to set calibration: %d", ret);
        return MGMT_ERR_EUNKNOWN;
    }

    ret = mag_cal_save();
    if (ret != 0) {
        LOG_ERR("Failed to save calibration: %d", ret);
        return MGMT_ERR_EUNKNOWN;
    }

    /* Build success response */
    ok = zcbor_tstr_put_lit(zse, "success") &&
         zcbor_bool_put(zse, true) &&
         zcbor_tstr_put_lit(zse, "offset_x") &&
         zcbor_int32_put(zse, cal.offset_x) &&
         zcbor_tstr_put_lit(zse, "offset_y") &&
         zcbor_int32_put(zse, cal.offset_y) &&
         zcbor_tstr_put_lit(zse, "offset_z") &&
         zcbor_int32_put(zse, cal.offset_z) &&
         zcbor_tstr_put_lit(zse, "scale_x") &&
         zcbor_uint32_put(zse, cal.scale_x) &&
         zcbor_tstr_put_lit(zse, "scale_y") &&
         zcbor_uint32_put(zse, cal.scale_y) &&
         zcbor_tstr_put_lit(zse, "scale_z") &&
         zcbor_uint32_put(zse, cal.scale_z);

    if (!ok) {
        return MGMT_ERR_EMSGSIZE;
    }

    LOG_INF("Mag cal set and saved: offsets=[%d,%d,%d], scales=[%u,%u,%u]",
            cal.offset_x, cal.offset_y, cal.offset_z,
            cal.scale_x, cal.scale_y, cal.scale_z);

    return 0;
}

/* Command handlers table */
static const struct mgmt_handler tempo_mgmt_handlers[] = {
    [TEMPO_MGMT_ID_SESSION_LIST] = {
        .mh_read = tempo_mgmt_session_list,
        .mh_write = NULL,
    },
    [TEMPO_MGMT_ID_SESSION_INFO] = {
        .mh_read = NULL,  /* TODO: Implement */
        .mh_write = NULL,
    },
    [TEMPO_MGMT_ID_STORAGE_INFO] = {
        .mh_read = tempo_mgmt_storage_info,
        .mh_write = NULL,
    },
    [TEMPO_MGMT_ID_LED_CONTROL] = {
        .mh_read = NULL,
        .mh_write = tempo_mgmt_led_control,  
    },
    [TEMPO_MGMT_ID_LOGGER_CONTROL] = {
        .mh_read = NULL,
        .mh_write = tempo_mgmt_logger_control,  
    },
    [TEMPO_MGMT_ID_SESSION_DELETE] = {
        .mh_read = NULL,
        .mh_write = tempo_mgmt_session_delete,
    },
    [TEMPO_MGMT_ID_SETTINGS_GET] = {
        .mh_read = tempo_mgmt_settings_get,
        .mh_write = NULL,
    },
    [TEMPO_MGMT_ID_SETTINGS_SET] = {
        .mh_read = NULL,
        .mh_write = tempo_mgmt_settings_set,
    },
    [TEMPO_MGMT_ID_GET_DATETIME] = {
        .mh_read = tempo_mgmt_get_datetime,
        .mh_write = NULL,
    },
    [TEMPO_MGMT_ID_TEST_LOGGING] = {
        .mh_read = NULL,
        .mh_write = tempo_mgmt_test_logging,
    },
    [TEMPO_MGMT_ID_MAG_CAL_GET] = {
        .mh_read = tempo_mgmt_mag_cal_get,
        .mh_write = NULL,
    },
    [TEMPO_MGMT_ID_MAG_CAL_SET] = {
        .mh_read = NULL,
        .mh_write = tempo_mgmt_mag_cal_set,
    },
};

static struct mgmt_group tempo_mgmt_group = {
    .mg_handlers = tempo_mgmt_handlers,
    .mg_handlers_count = ARRAY_SIZE(tempo_mgmt_handlers),
    .mg_group_id = MGMT_GROUP_ID_TEMPO,
};

/* Register custom handlers */
void tempo_mgmt_register(void)
{
    mgmt_register_group(&tempo_mgmt_group);
    LOG_INF("Tempo custom mcumgr handlers registered (group=%d, count=%d)",
            MGMT_GROUP_ID_TEMPO, (int)ARRAY_SIZE(tempo_mgmt_handlers));
}
